jburks/vera-module/programmer/win/vera_programmer_win/lib.h

#pragma once

#include <sys/types.h>
#include <sys/stat.h>
#include <fcntl.h>
#include <signal.h>
#include <stdbool.h>
#include <stdint.h>
#include <stdio.h>
#include <stdlib.h>
#include <string.h>

void hexdump(const void* buf, int length);
